Vincent-Flotron/Stairs/ListeDeMateriel.pdf

Sheet1

Description | Matériau et dimensions [mm] | Quantité en barres de [6m]
Barrières | Acier plat 10x40 | 15
Fix marches | Acier plat 8x50 | 12
Limons | Acier plat 15x250 | 8
Fix. Limonx | Acier plat 80x12 | 1
Fix. Barrières | Acier plat 90x10 | 1
Fix. Main courante | Acier plat 14x4 (si pas 14x4 alors 15x4) | 1
Barreaux | Acier rond Diam10 | 15
Description | Matériau et dimensions [mm] | Quantité [pce]
Vis Fix. Limons | Vis acier zingué 6 pans extérieur M16x50 | 35
| Ecrous acier zingué 6 pans M16 | 35
| Rondelles acier zingué ressort M16 | 35
| Rondelles acier zingué plates M16 | 70
Vis fix barrières | Vis acier zingué 6 pans extérieur M10x35 | 25
| Rondelles acier zingué ressort M10 | 25
| Rondelles acier zingué plates M10 | 25

Liste de matériel :

Date : 16.04.2024
