Vincent-Flotron/Stairs/dxf/Limon1er2emePalier.dxf

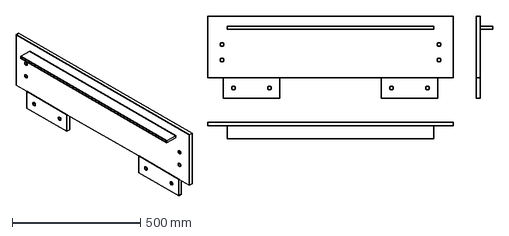
[picture p18: CAD file, 2025-02-08]
dxf/Limon1er2emePalier.dxf
1857.0 x 699.3 mm
