Vincent-Flotron/Stairs/dxf/Epaiss12mm/LimonRez1ereVoleeBasGauche_V2.dxf

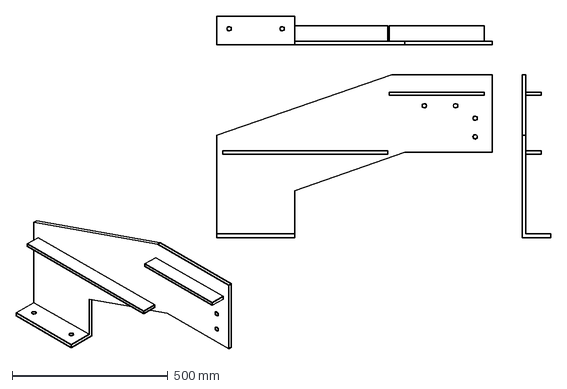
[picture p19: CAD file, 2025-03-16]
dxf/Epaiss12mm/LimonRez1ereVoleeBasGauche_V2.dxf
1716.0 x 1067.8 mm
