Vincent-Flotron/Stairs/dxf/LimonRez2emeVoleeDroite.dxf

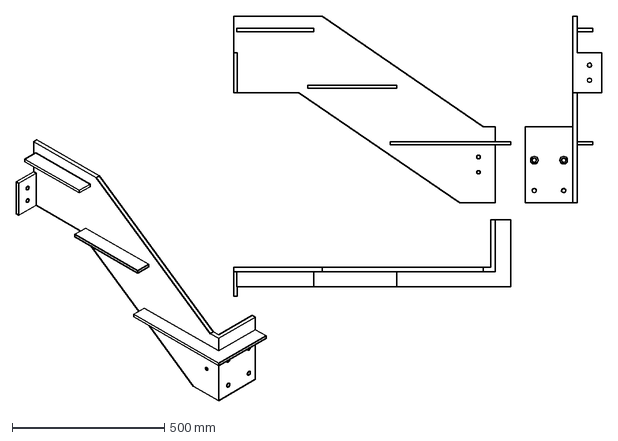
[picture p20: CAD file, 2025-02-08]
dxf/LimonRez2emeVoleeDroite.dxf
1920.2 x 1260.9 mm
