Vincent-Flotron/Stairs/dxf/Epaiss12mm/BarriereRez1ereVoleeBasGauche_V2.dxf

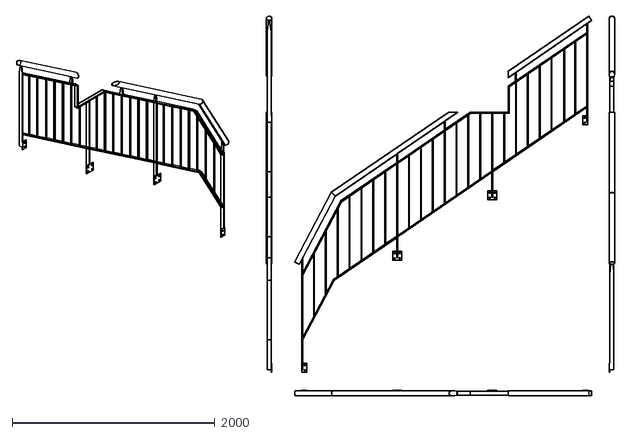
[picture p21: CAD file, 2025-03-16]
dxf/Epaiss12mm/BarriereRez1ereVoleeBasGauche_V2.dxf
5902.7 x 3747.9
