Vincent-Flotron/Stairs/dxf/LimonRez1ereVoleeDroite.dxf

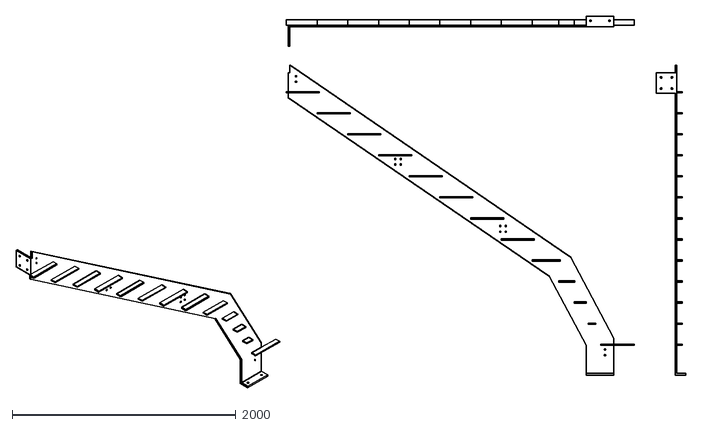
[picture p22: CAD file, 2025-02-08]
dxf/LimonRez1ereVoleeDroite.dxf
5988.1 x 3322.3
