Vincent-Flotron/Stairs/dxf/Barriere1er2emeVolee.dxf

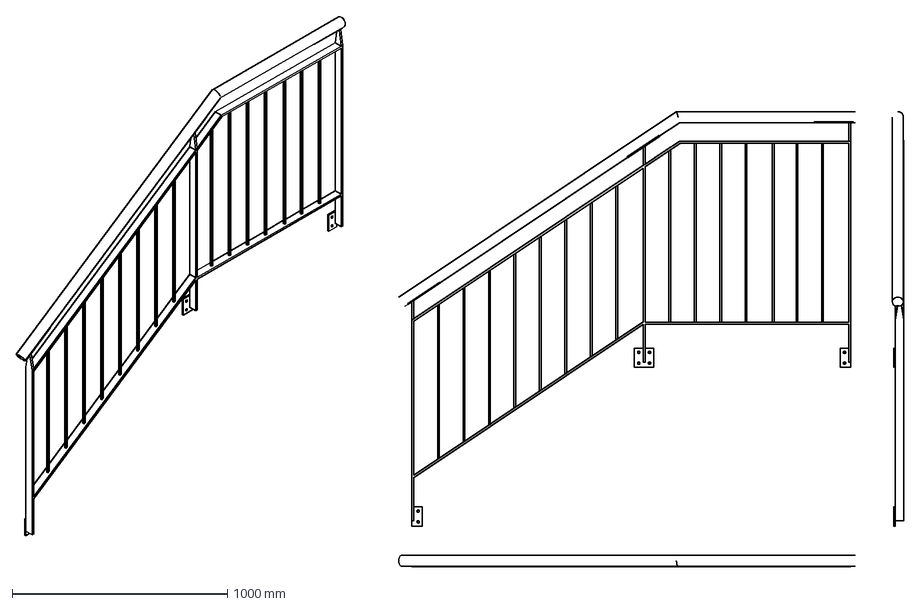
[picture p23: CAD file, 2025-02-08]
dxf/Barriere1er2emeVolee.dxf
4128.6 x 2560.4 mm
