Vincent-Flotron/Stairs/dxf/Epaiss12mm/Barriere1er2emeVolee_V2.dxf

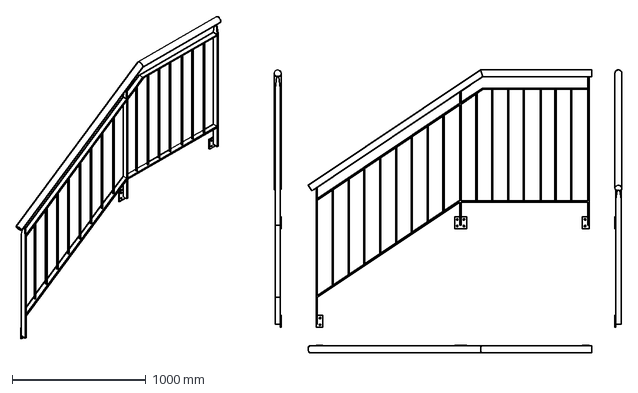
[picture p24: CAD file, 2025-03-16]
dxf/Epaiss12mm/Barriere1er2emeVolee_V2.dxf
4535.1 x 2517.8 mm
