Vincent-Flotron/Stairs/dxf/BarriereRez2emeVolee.dxf

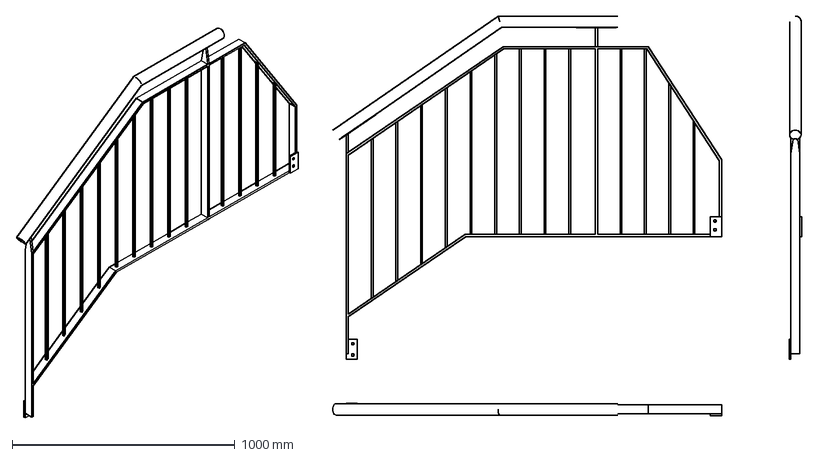
[picture p25: CAD file, 2025-02-08]
dxf/BarriereRez2emeVolee.dxf
3526.2 x 1804.5 mm
