Vincent-Flotron/Stairs/dxf/Epaiss12mm/LimonRez1ereVoleeGauche_V2.dxf

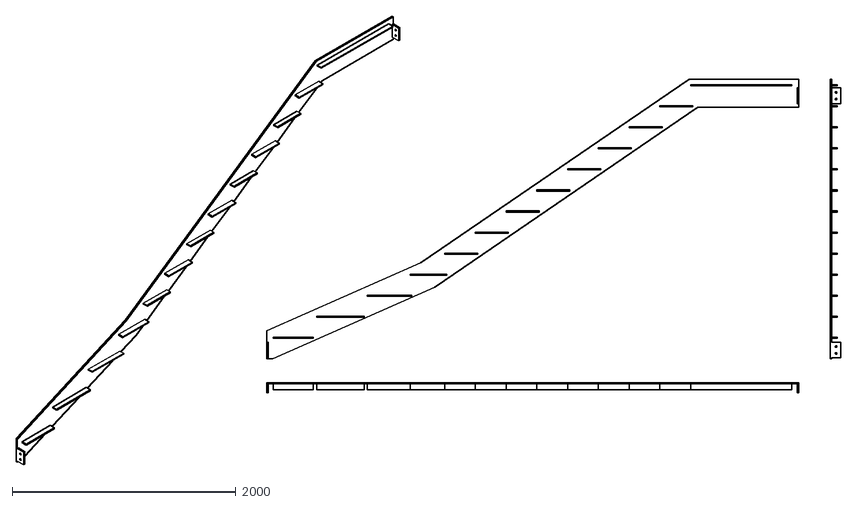
[picture p26: CAD file, 2025-03-16]
dxf/Epaiss12mm/LimonRez1ereVoleeGauche_V2.dxf
7360.3 x 4009.1
