Vincent-Flotron/Stairs/dxf/Epaiss12mm/Limon1er1ereVoleeGauche_V2.dxf

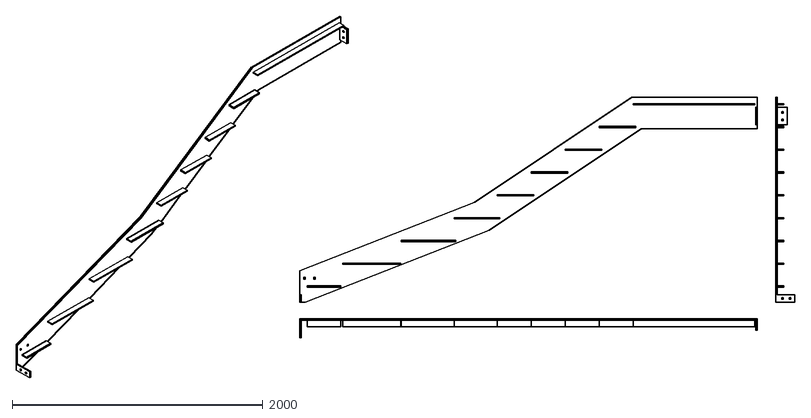
[picture p27: CAD file, 2025-03-16]
dxf/Epaiss12mm/Limon1er1ereVoleeGauche_V2.dxf
6214.4 x 2888.2
