Vincent-Flotron/Stairs/dxf/Limon1er1ereVoleeDroite.dxf

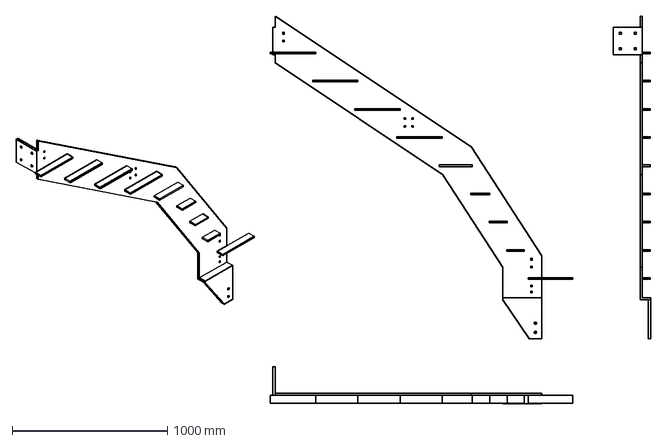
[picture p28: CAD file, 2025-02-08]
dxf/Limon1er1ereVoleeDroite.dxf
4089.6 x 2498.9 mm
