Vincent-Flotron/Stairs/dxf/Epaiss12mm/Barriere1er1ereVolee_V2.dxf

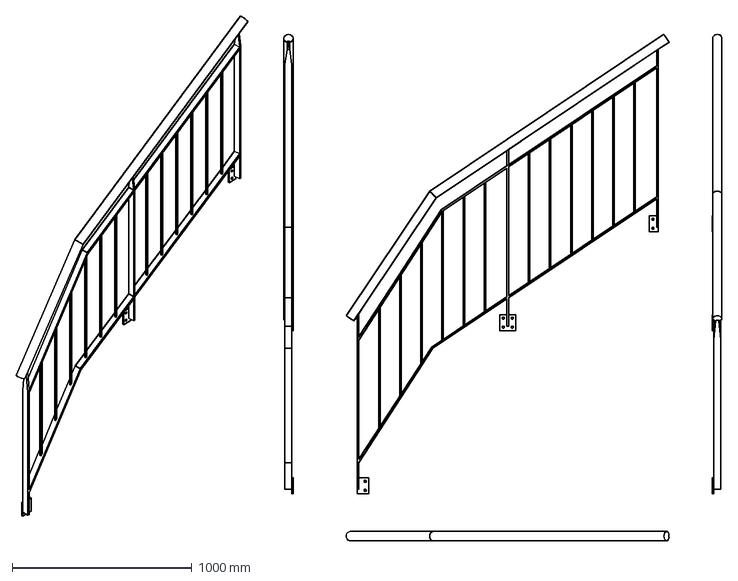
[picture p29: CAD file, 2025-03-16]
dxf/Epaiss12mm/Barriere1er1ereVolee_V2.dxf
3922.9 x 2915.3 mm
