Vincent-Flotron/Stairs/dxf/Limon1erPalier.dxf

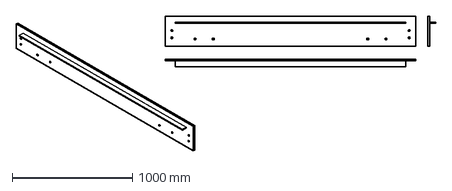
[picture p30: CAD file, 2025-02-08]
dxf/Limon1erPalier.dxf
3491.5 x 1120.2 mm
