Vincent-Flotron/Stairs/dxf/Epaiss12mm/Limon1er2emeVoleeDroite_V2.dxf

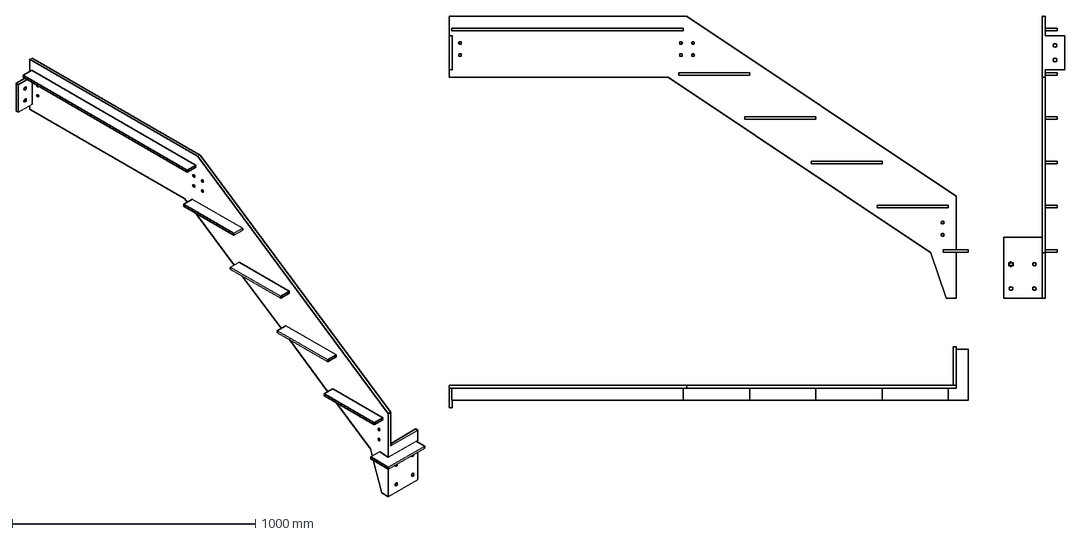
[picture p31: CAD file, 2025-03-16]
dxf/Epaiss12mm/Limon1er2emeVoleeDroite_V2.dxf
4308.4 x 1974.9 mm
