Vincent-Flotron/Stairs/dxf/LimonRez1ereVoleeBasGauche.dxf

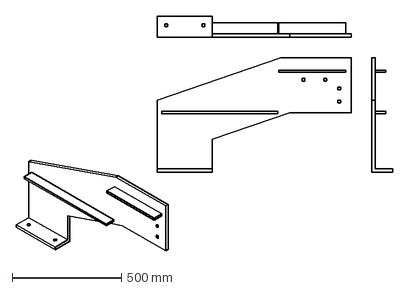
[picture p32: CAD file, 2025-02-08]
dxf/LimonRez1ereVoleeBasGauche.dxf
1718.5 x 1069.9 mm
