Vincent-Flotron/Stairs/dxf/Epaiss12mm/Limon1er2emePalier_V2.dxf

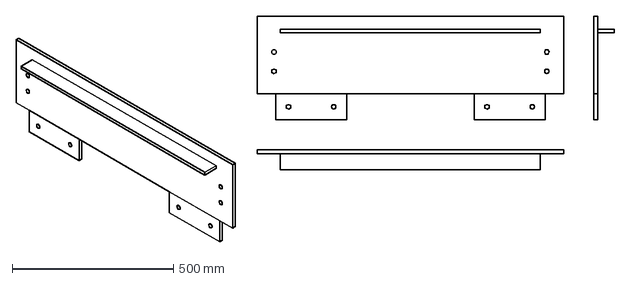
[picture p33: CAD file, 2025-03-16]
dxf/Epaiss12mm/Limon1er2emePalier_V2.dxf
1852.3 x 697.5 mm
