Vincent-Flotron/Stairs/dxf/Limon1er2emeVoleeGauche.dxf

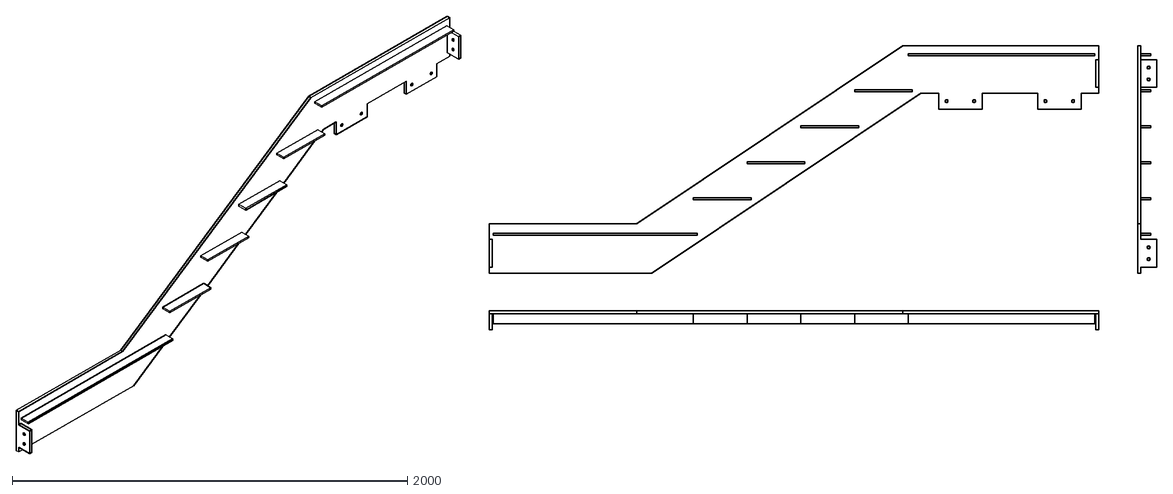
[picture p34: CAD file, 2025-02-08]
dxf/Limon1er2emeVoleeGauche.dxf
5766.8 x 2211.3
