Vincent-Flotron/Stairs/dxf/Epaiss12mm/Vue_Générale.dxf

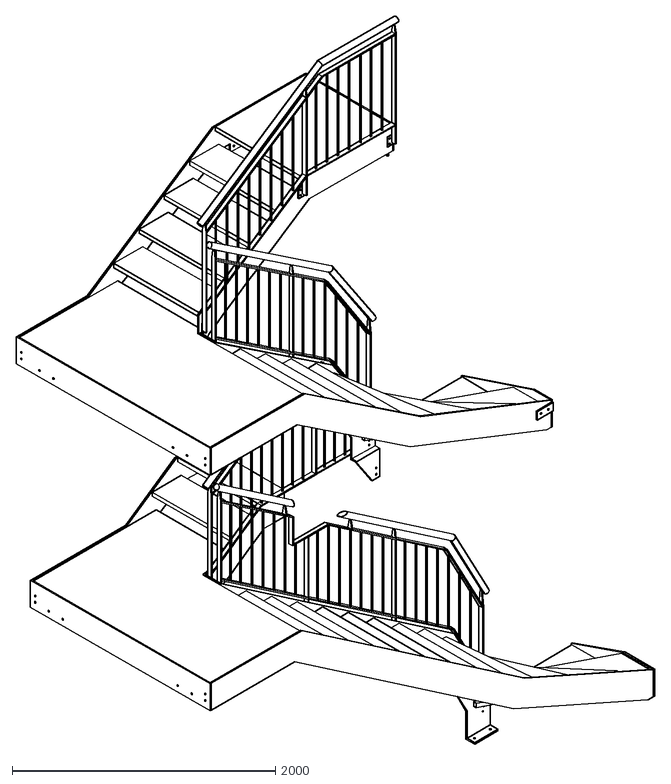
[picture p35: CAD file, 2025-03-16]
dxf/Epaiss12mm/Vue_Générale.dxf
4847.9 x 5530.8
