Vincent-Flotron/Stairs/dxf/Limon1er1ereVoleeGauche.dxf

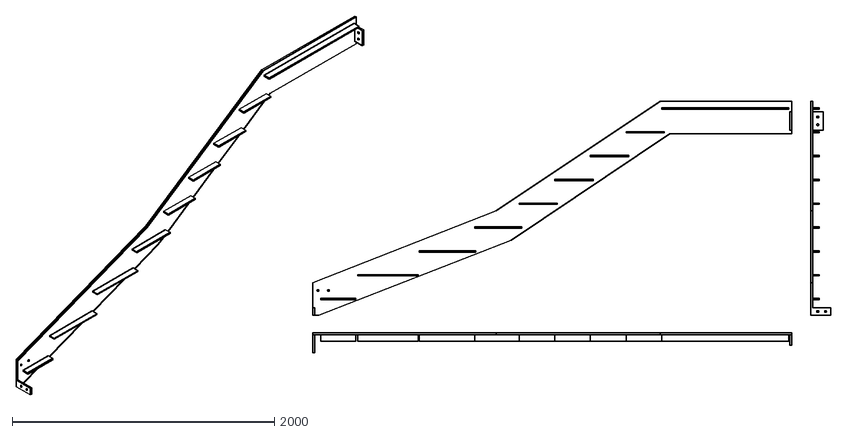
[picture p36: CAD file, 2025-02-08]
dxf/Limon1er1ereVoleeGauche.dxf
6216.9 x 2889.4
