Vincent-Flotron/Stairs/dxf/Barriere1er1ereVolee.dxf

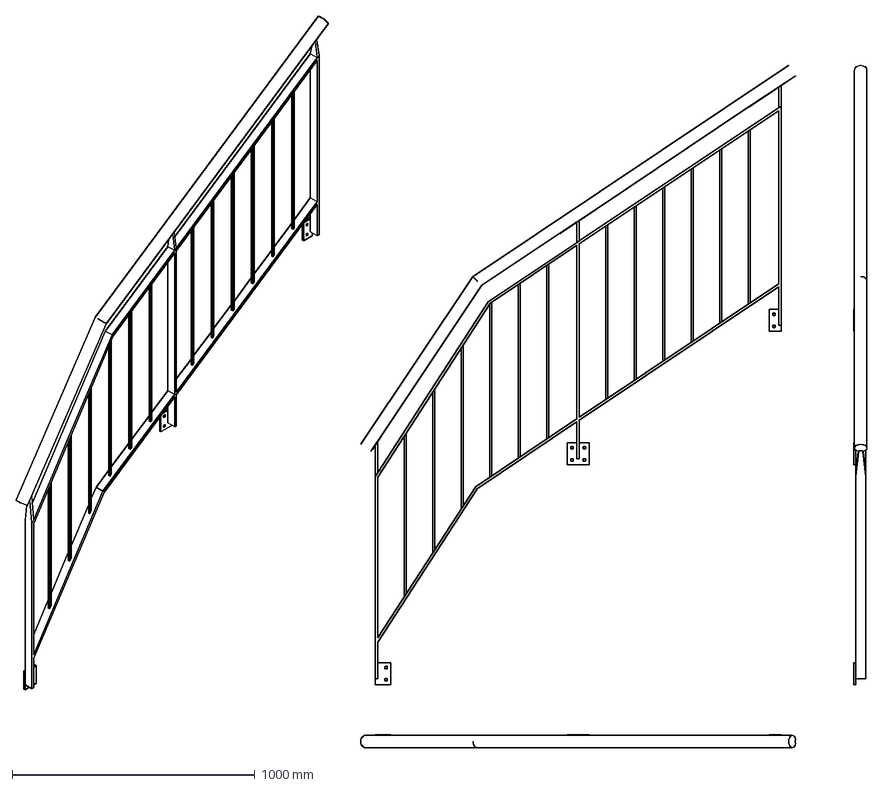
[picture p37: CAD file, 2025-02-08]
dxf/Barriere1er1ereVolee.dxf
3508.6 x 3016.4 mm
