Vincent-Flotron/Stairs/dxf/Epaiss12mm/Limon1er1ereVoleeDroite_V2.dxf

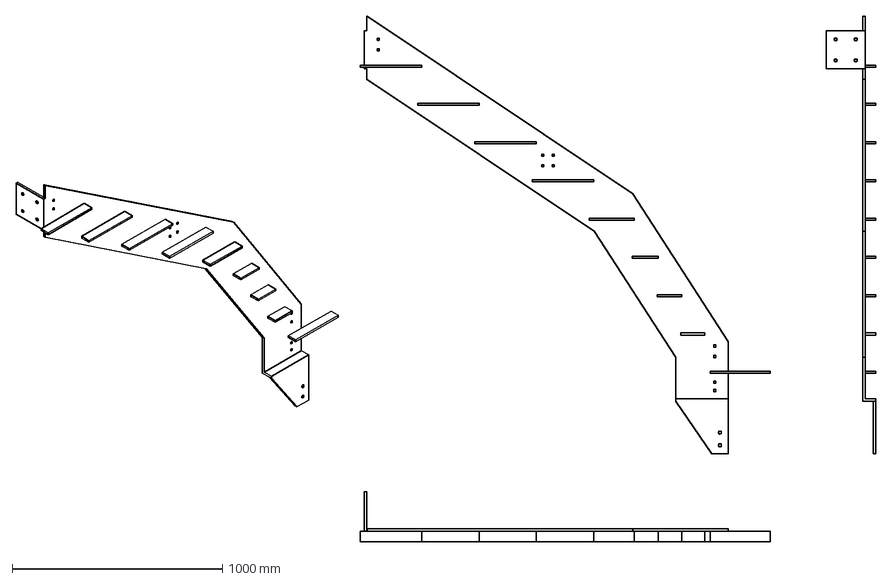
[picture p38: CAD file, 2025-03-16]
dxf/Epaiss12mm/Limon1er1ereVoleeDroite_V2.dxf
4086.5 x 2497.4 mm
