Vincent-Flotron/Stairs/dxf/Epaiss12mm/LimonRezPalier_V2.dxf

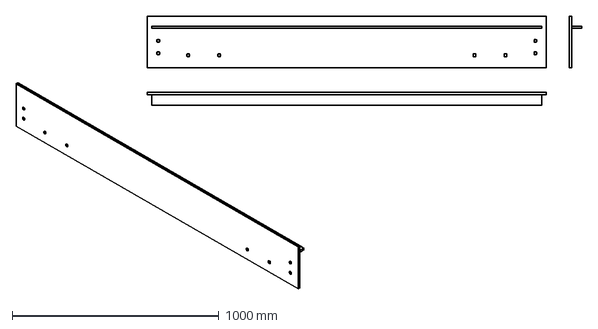
[picture p39: CAD file, 2025-03-16]
dxf/Epaiss12mm/LimonRezPalier_V2.dxf
2738.6 x 1320.9 mm
