Vincent-Flotron/Stairs/dxf/Epaiss12mm/Limon1er1ereVoleeBasGauche_V2.dxf

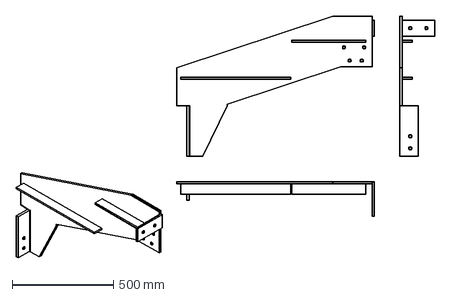
[picture p40: CAD file, 2025-03-16]
dxf/Epaiss12mm/Limon1er1ereVoleeBasGauche_V2.dxf
2067.6 x 1196.3 mm
