Vincent-Flotron/Stairs/M5.pdf

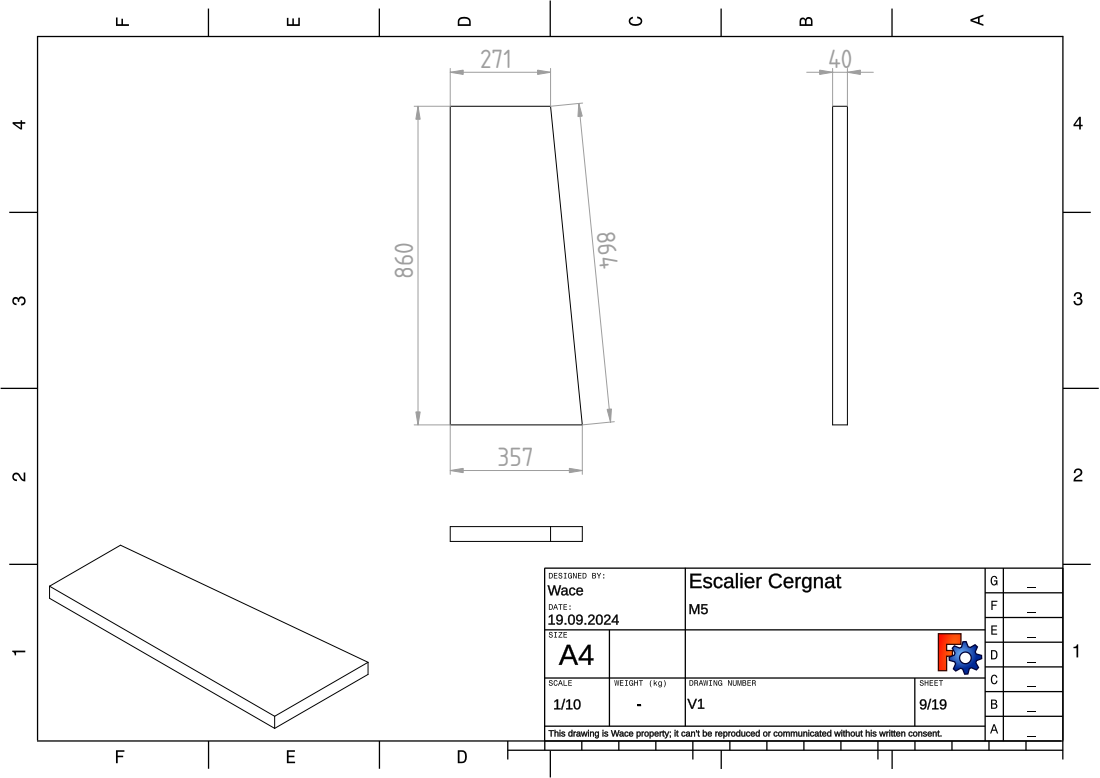
[picture p55: page 1]
