Vincent-Flotron/Stairs/M5_diag.pdf

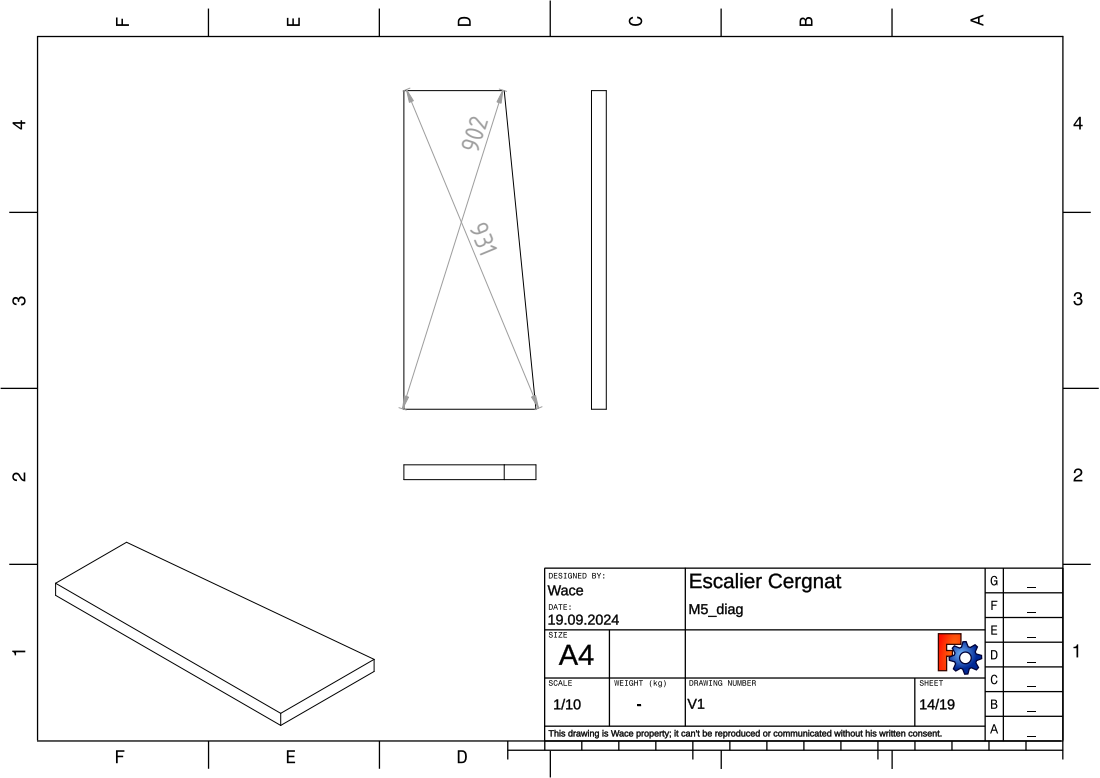
[picture p56: page 1]
