Vincent-Flotron/Stairs/M6-M13.pdf

315 40

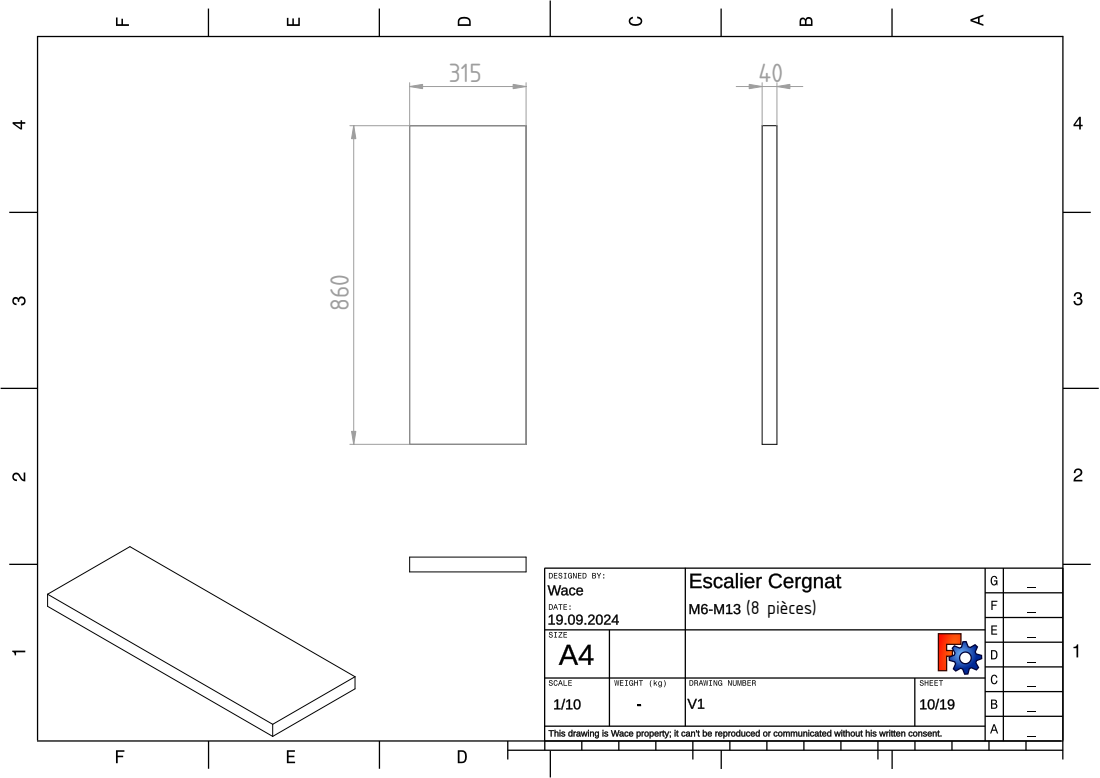
[picture p57: page 1]
(8 pièces)
