Vincent-Flotron/Stairs/M6-M13_diag.pdf

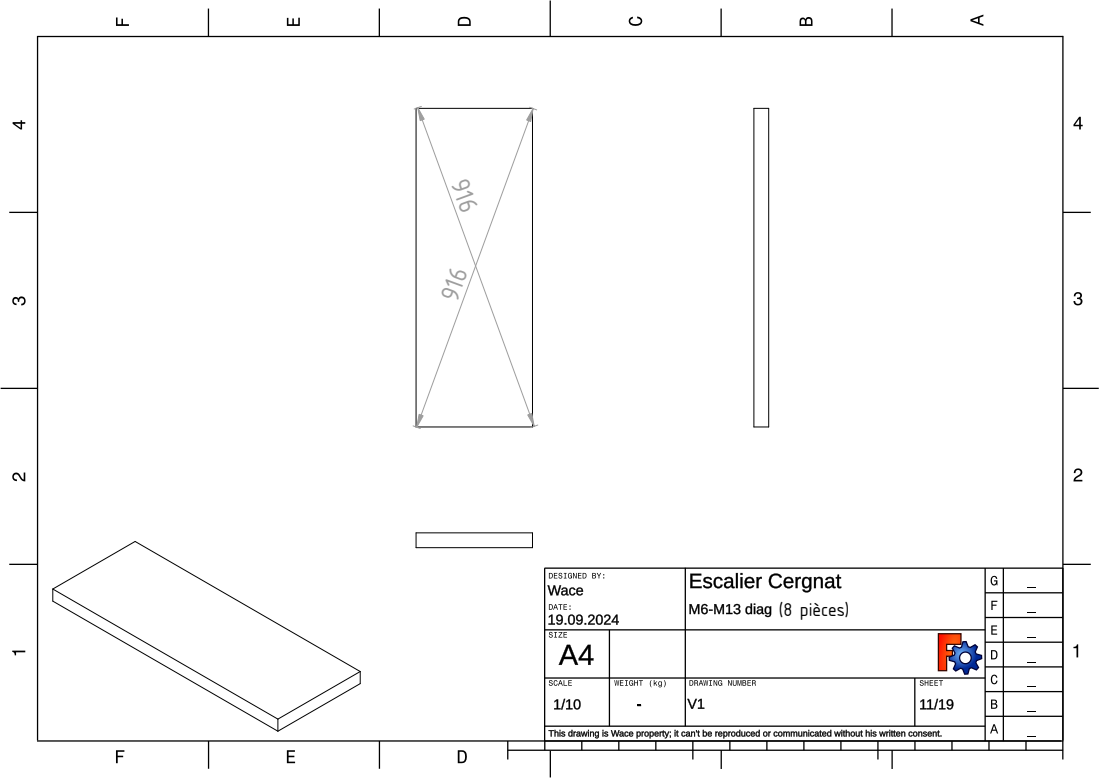
[picture p58: page 1]
(8 pièces)
