Vincent-Flotron/Stairs/N1.pdf

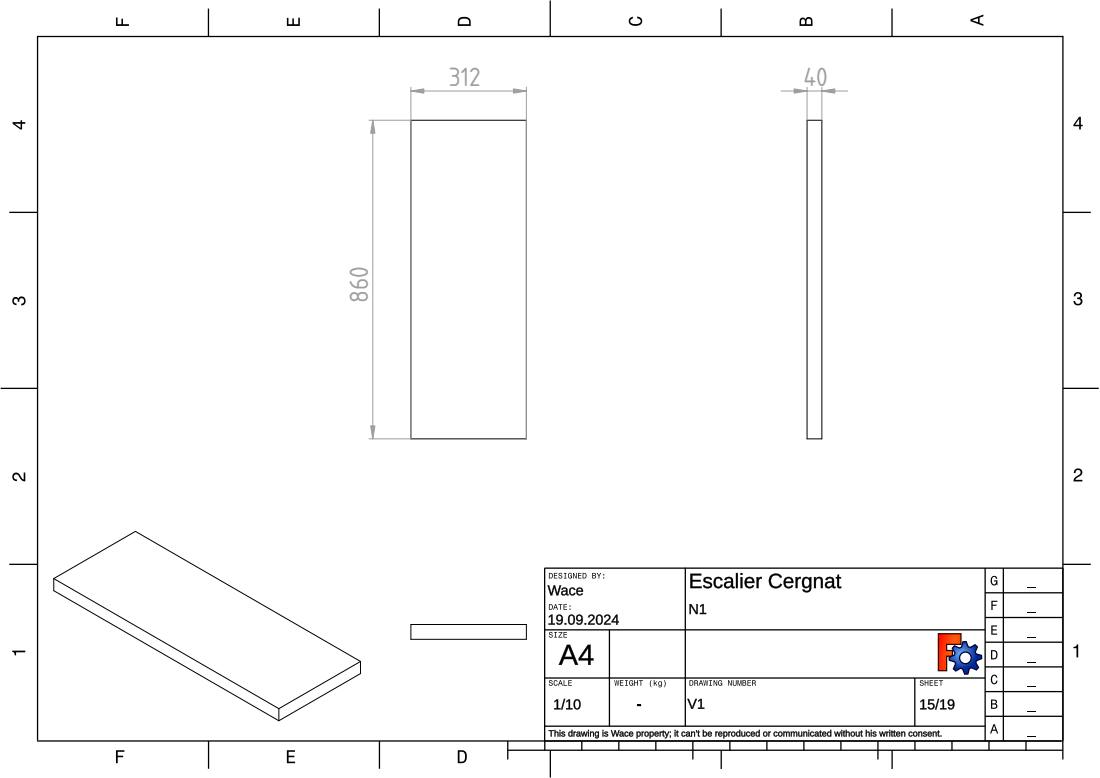
[picture p59: page 1]
