Vincent-Flotron/Stairs/N1_diag.pdf

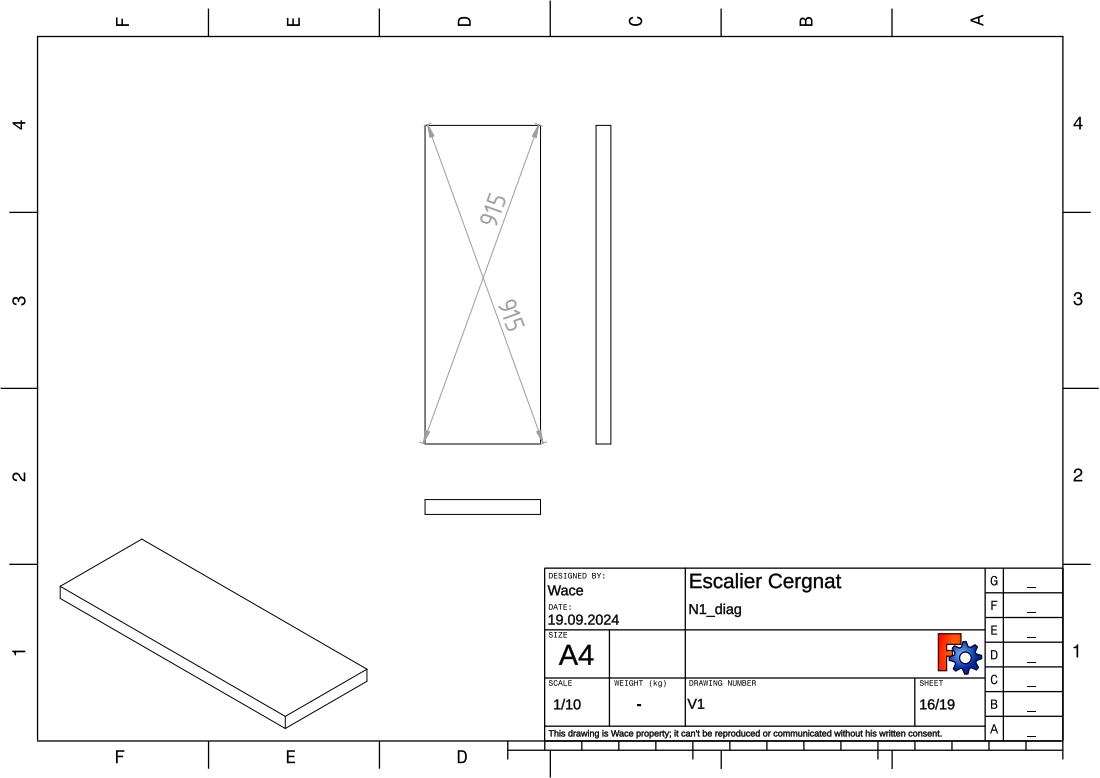
[picture p60: page 1]
