Vincent-Flotron/Stairs/N2.pdf

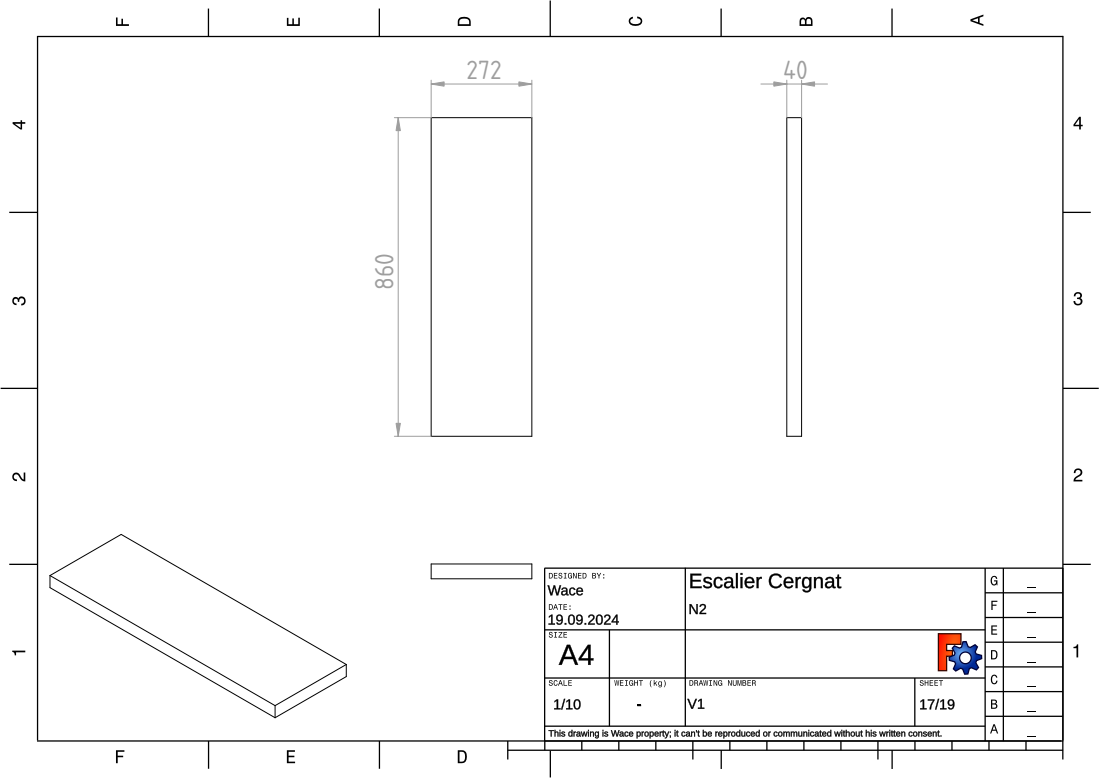
[picture p61: page 1]
