Vincent-Flotron/Stairs/N2_diag.pdf

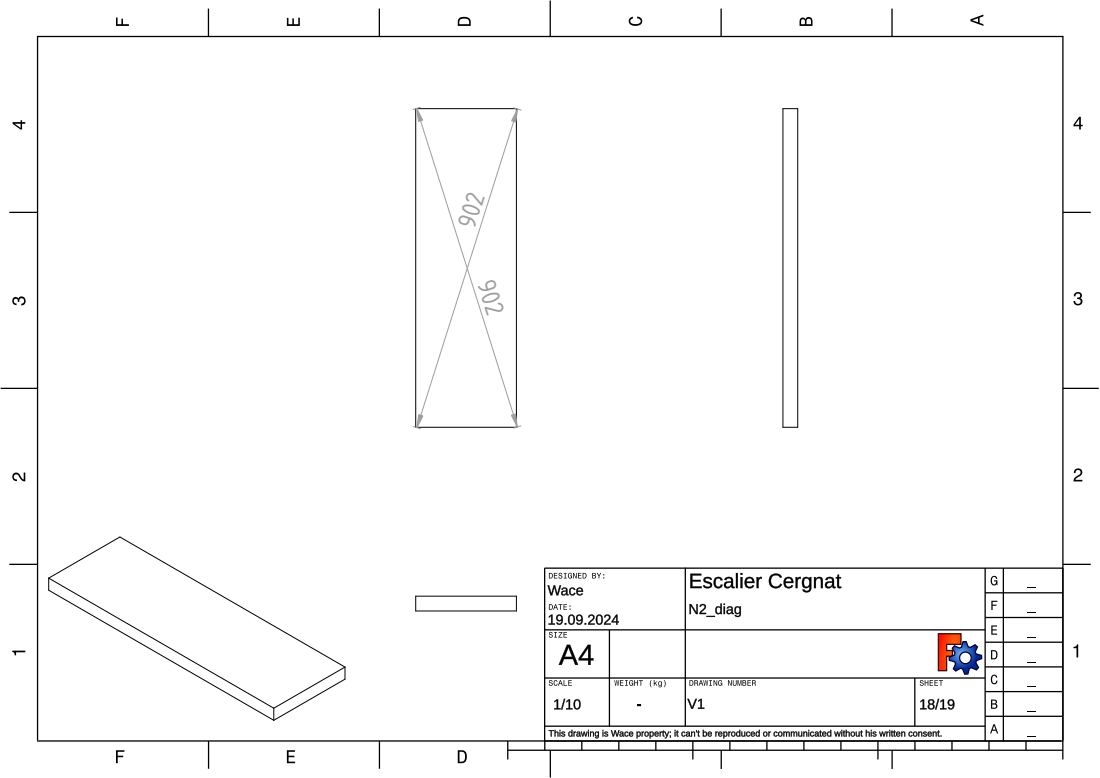
[picture p62: page 1]
