Vincent-Flotron/Stairs/PiedsEscaliers.pdf

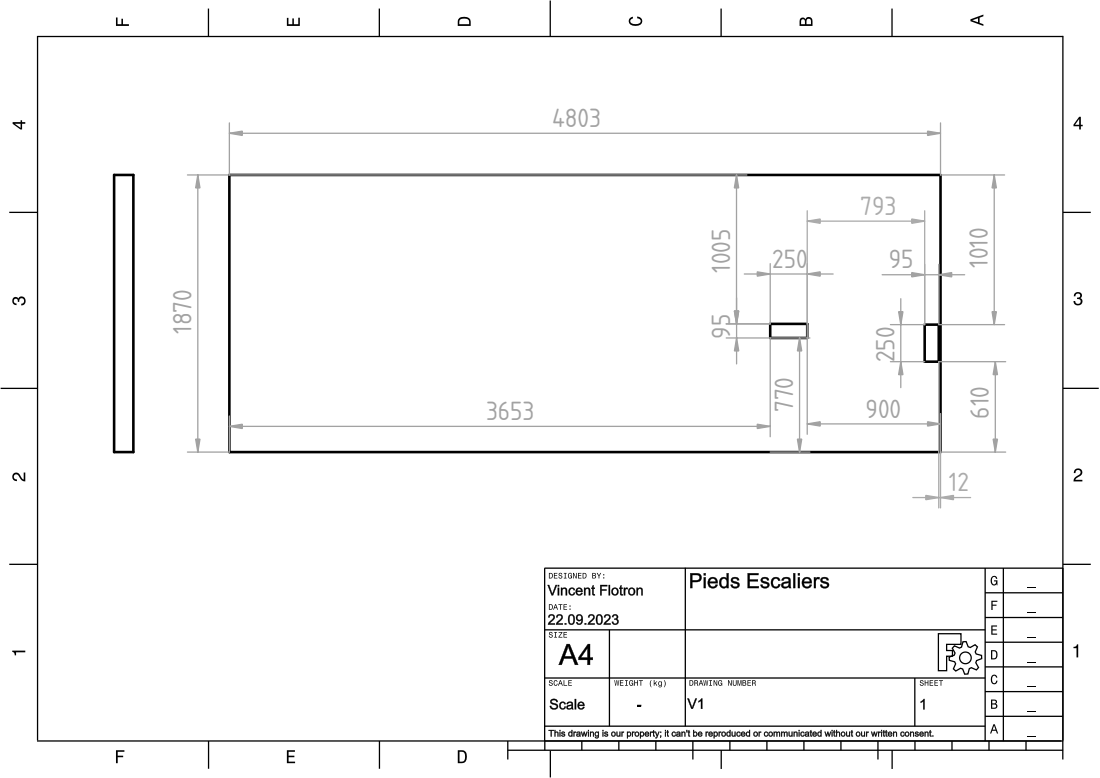
[picture p63: page 1]
