Vincent-Flotron/Stairs/Vue pour hauteurs fenêtre.pdf

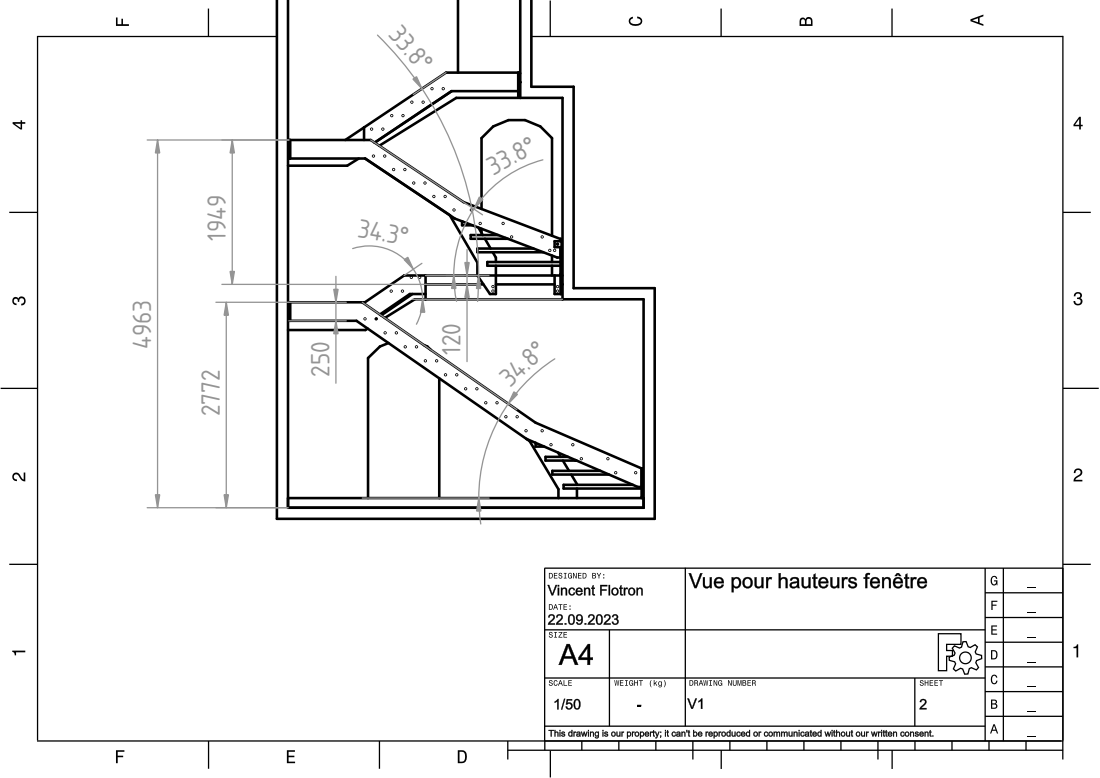
[picture p64: page 1]
